GauravAnandIITG/T-Magnus-Aircraft/WhatsApp Image 2025-09-02 at 19.15.59_cc875ce8.jpg

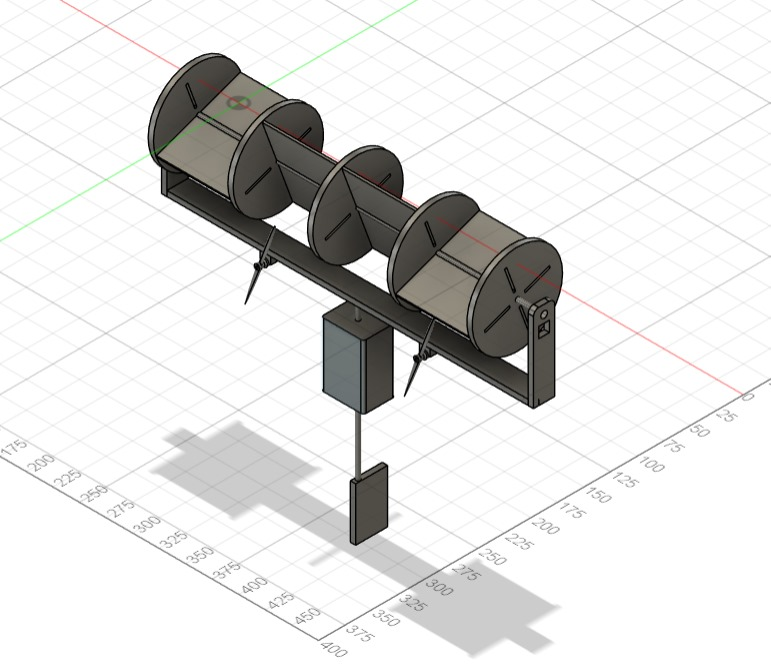
WhatsApp Image 2025-09-02 at 19.15.59_cc875ce8.jpg
